loopyengineeringco/Daly2Sofar/Daly2Sofar Node-Red to HA example.jpg

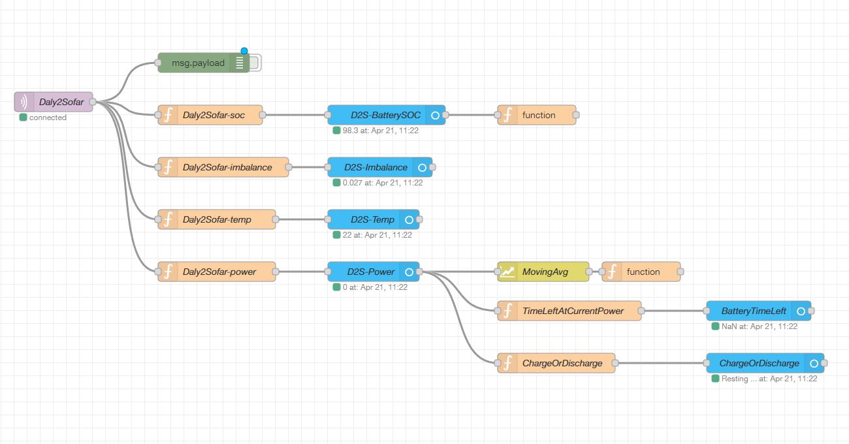
Daly2Sofar Node-Red to HA example.jpg
