loopyengineeringco/Daly2Sofar/3D Printables/Top_slicer.JPG

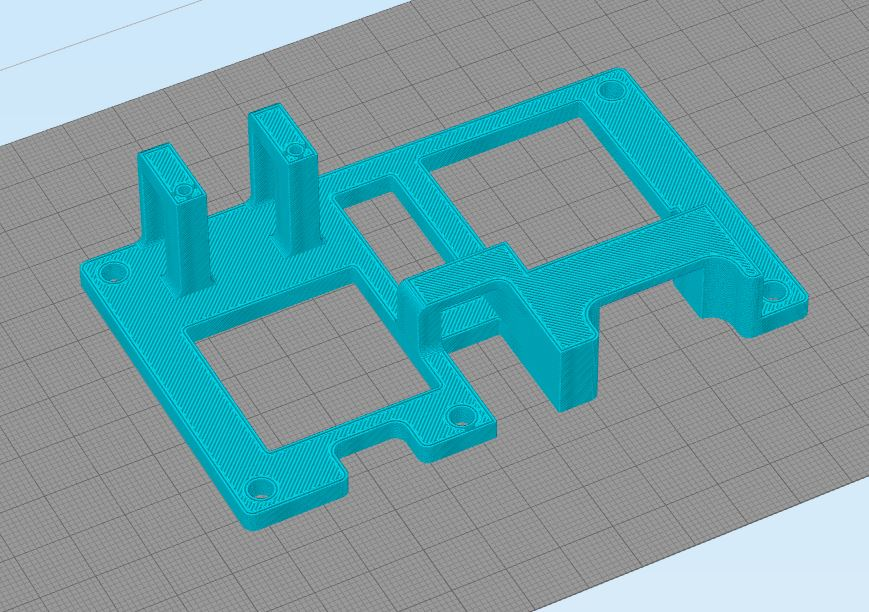
3D Printables/Top_slicer.JPG
